bekuz007/hydrodesk-base/doku/Steckbrief_HydroDesk_Base.docx

Steckbrief zu Projekt HydroDesk Base

Betreuer: ________________ Gruppenmitglieder: _______________________________________________________

Problem / Szenario / Projekt:

Welches Thema? Wie lautet die Projektidee?
Wo begegnet mir das Thema / Problem in meinem Alltag?

Thema: IoT-Schreibtisch-Gadget zur Trinkmengen-Erfassung (HydroDesk Base).

Projektidee: Ein flaches, rechteckiges ESP32-Gerät (180 × 100 × 25 mm) für den Schreibtisch. Links sitzt das Board CYD ESP32-2432S028R mit 2,8″-Touch-Display, rechts ein Flaschen-Pad (90 × 90 mm) mit Silikonmatte für jede normale Flasche. Eine Wägezelle misst das Gewicht; per Touch-Tasten „Leer“ und „Voll“ wird die Flasche kalibriert und die getrunkene Menge in ml berechnet. Das Display zeigt Tagesziel, Fortschritt und nächste Erinnerung, eine Lichtlinie vorne (COB-LED-Streifen hinter gedrucktem Diffusor) erinnert ans Trinken. Bei verschüttetem Wasser schaltet ein Feuchtigkeitssensor den Strom ab, ein Schalter trennt den Akku ab. Per Bluetooth LE verbindet sich das Gerät mit einer Android-App (Supabase). Optional: Telegram.

Alltag: Am Schreibtisch oder in der Schule steht die Flasche oft da, aber man vergisst zu trinken. Fertige Smart-Flaschen sind teuer und an eine Marke gebunden. HydroDesk Base funktioniert mit jeder Flasche und ist täglich sichtbar.

Handlungsprodukt:

Was ist das Endprodukt? Welche Konfigurationen sollen am Ende gemacht sein?

Endprodukt: Funktionsfähiger Prototyp im 3D-gedruckten Gehäuse (Display links, Flaschen-Pad rechts, Lichtlinie vorne, Ein/Aus-Schalter links, abnehmbare USB-Kappe), live vorführbar, plus Android-App, Quellcode im Git-Repo, CAD-Datei, Lasten-/Pflichtenheft, Testprotokoll und Bericht.

Am Ende konfiguriert:

• WLAN und optional Telegram-Token in secrets.h (nicht im Repo), BLE-Kopplung zur App

• Flaschen-Kalibrierung per Touch: „Leer“ (leere Flasche) und „Voll“ (volle Flasche)

• Kalibrierung der Wägezelle (Tara, Leer- und Vollgewicht dauerhaft speichern)

• Feuchtigkeits-Schwelle: bei Nässe → LED-Strom aus und Sperrbildschirm „WASSER ERKANNT · STROM AUS“

• Lichtlinie vorne (COB-LED-Streifen WS2812B, 26 LEDs, Diffusor): blau = Erinnerung, grün = Ziel erreicht, rot = Akku / Fehler, bei Nässe aus

• Optional Bot-Befehle: /status, /ziel, /hilfe

Gruppenzusammensetzung

Wie viele Schüler werden gemeinsam an dem Projekt arbeiten?
Wer könnte welche Aufgabe übernehmen?

2 Schüler, ca. 50 Stunden inkl. Dokumentation (je 25 h).

Person A: Hardware, Verkabelung, Wägezelle (HX711), Feuchtigkeitssensor, Stromversorgung (LiPo, USB-C, Ein/Aus-Schalter, Sicherheitsabschaltung), rechteckiges Gehäuse (CAD + 3D-Druck), Zustandsautomat.

Person B: Touch-Display und Bedienoberfläche, WLAN/NTP, optionale Telegram-Anbindung, Leer/Voll-Kalibrierung, Doku-Leitung.

Gemeinsam: Planung, Integration, Tests, Bericht, Präsentation.

Konkretisierung der Inhalte

Welche einzelnen Inhalte sind relevant?
Welche Konfigurationen / Techniken werden angewandt?
Welche Schritte werden erwartet?
Was ist die Ziel- / Endkonfiguration?

Inhalte: Mikrocontroller-Programmierung in C/C++, Sensorik (Wägezelle, Feuchtigkeitseingang), Touch-Bedienoberfläche, Zustandsautomat (UML), Bluetooth LE, Android-App, optional Telegram, Umgang mit Zugangsdaten, Git, CAD, Testen und Dokumentieren.

Techniken: PlatformIO (Arduino), CYD ESP32-2432S028R (2,8″-Touch), HX711 + Wägezelle 5 kg, COB-LED-Streifen WS2812B mit Diffusor, LiPo + TC4056/USB-C + Pololu S13V10F5, Nässe-Abschaltung (Regensensor + AO3401A), Ein/Aus-Schalter, Stromsparen, Bluetooth LE, Android-App (Kotlin, Supabase), OpenSCAD.

Schritte: 1. Lasten-/Pflichtenheft, Zustandsdiagramm 2. Entwicklungsumgebung, Sensor- und Display-Test 3. Wäge-Kalibrierung (Leer/Voll) 4. Feuchtigkeits-Sicherheitsabschaltung 5. Bedienoberfläche, Bluetooth LE + Android-App, optional Telegram 6. Gehäuse konstruieren, drucken, Integration 7. Tests 8. Doku und Präsentation

Zielkonfiguration: Gerät 180 × 100 × 25 mm mit Akku, USB-C-Laden und Ein/Aus-Schalter; Flasche abstellen → ml-Anzeige wenige Sekunden nach der Leer/Voll-Kalibrierung; bei Wasser Strom aus und Sperrbildschirm; Erinnerung per Lichtlinie, Daten per BLE in der App; Akkulaufzeit geschätzt ca. 27–54 h.

Benötigte Materialien

Welche Ausstattung benötigen die Schüler für die Durchführung?
Welche Materialien müssten seitens der Schule / des Betreuers gestellt werden?

Schüler: Laptop mit VS Code + PlatformIO, Android Studio, OpenSCAD; Android-Smartphone, Handy-Hotspot für die Demo, GitHub-Account.

Von Schule / Betreuer (ca. 142 € laut Vorkalkulation, ca. 125 € ohne PLA): CYD ESP32-2432S028R, Wägezelle 5 kg + HX711, COB-LED-Streifen, Regensensor, FET-Platine + Ein/Aus-Schalter, LiPo + TC4056 + Pololu S13V10F5, Silikonmatte, Kleinteile, Messschieber, Lötstation; 3D-Druck des Gehäuses; optional Breadboard.

Hinweis: Es wird keine Smart-Flasche gekauft – jede vorhandene Flasche dient zur Demo.
