bekuz007/hydrodesk-base/gehaeuse/preview/01_zusammenbau_iso.png

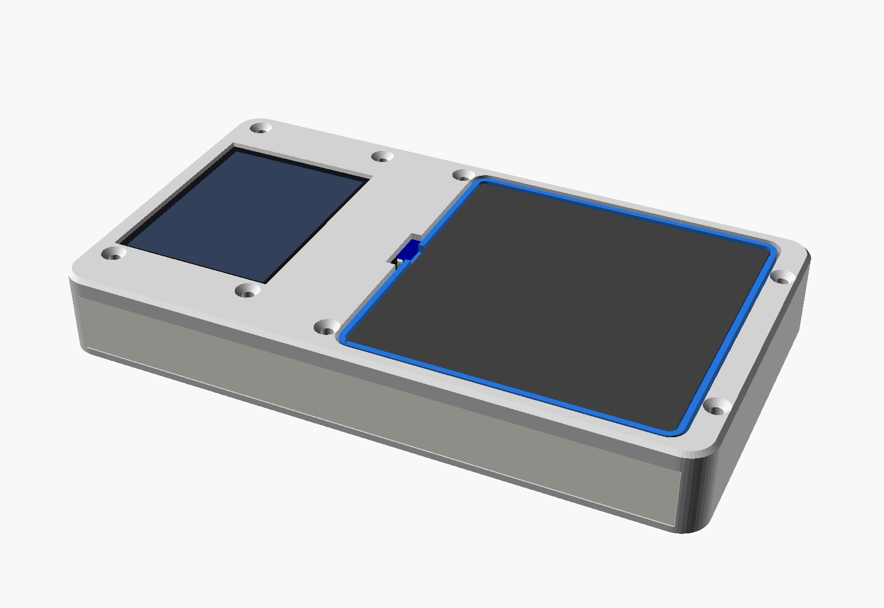
gehaeuse/preview/01_zusammenbau_iso.png
