bekuz007/hydrodesk-base/gehaeuse/preview/02_explosionsansicht.png

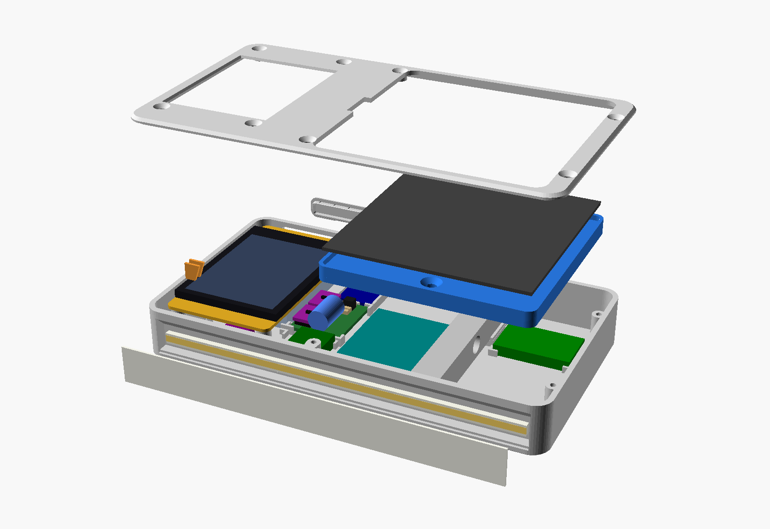
gehaeuse/preview/02_explosionsansicht.png
