bekuz007/hydrodesk-base/gehaeuse/preview/03_draufsicht.png

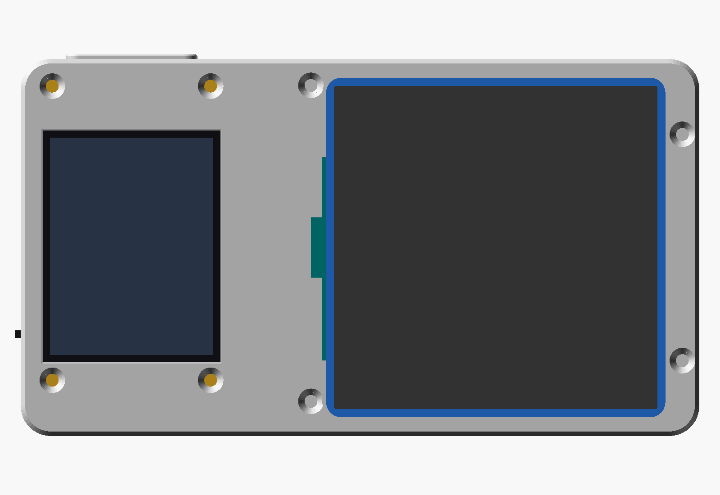
gehaeuse/preview/03_draufsicht.png
