bekuz007/hydrodesk-base/gehaeuse/preview/04_innen_ohne_deckel.png

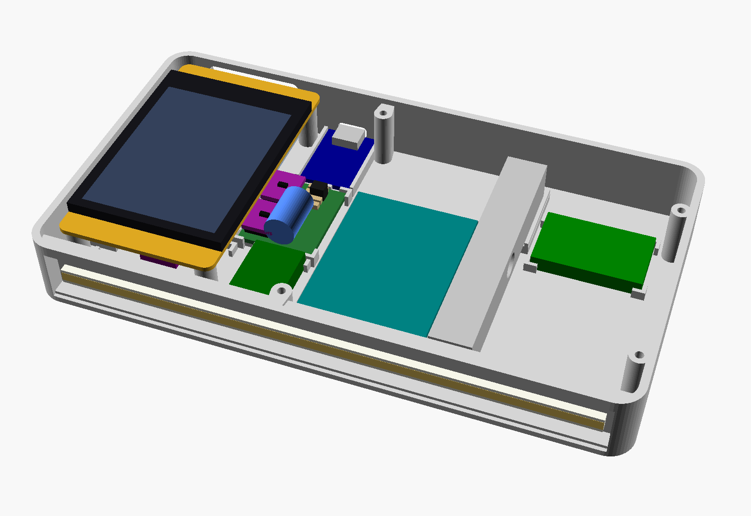
gehaeuse/preview/04_innen_ohne_deckel.png
