bekuz007/hydrodesk-base/gehaeuse/preview/05_innen_draufsicht.png

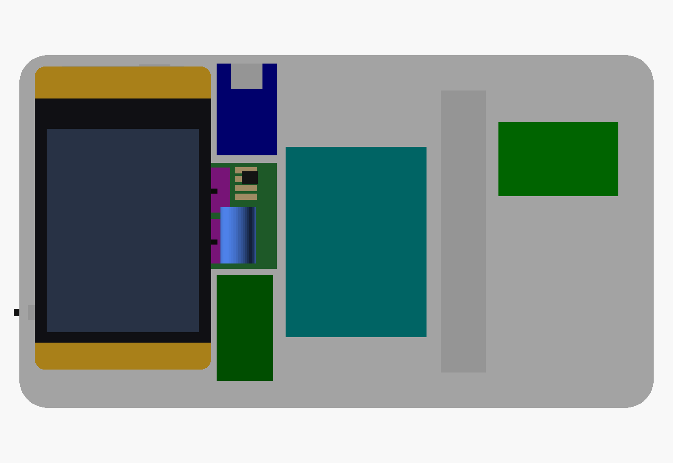
gehaeuse/preview/05_innen_draufsicht.png
