bekuz007/hydrodesk-base/gehaeuse/preview/06_rueckseite_usb.png

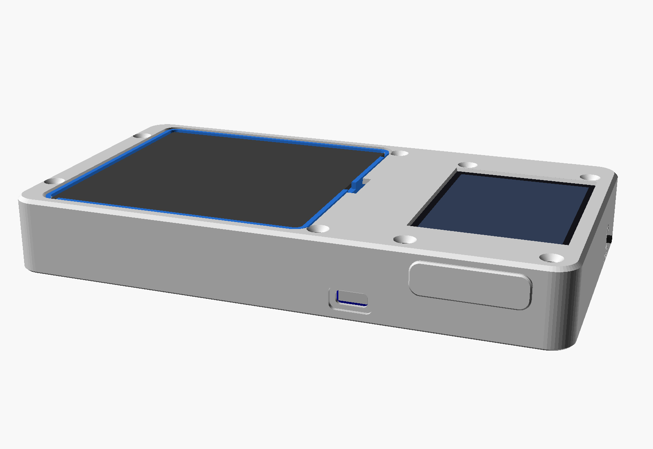
gehaeuse/preview/06_rueckseite_usb.png
