bekuz007/hydrodesk-base/gehaeuse/preview/07_front_led.png

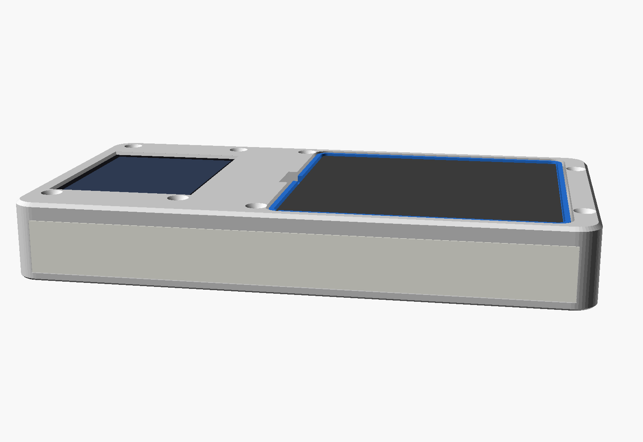
gehaeuse/preview/07_front_led.png
