bekuz007/hydrodesk-base/gehaeuse/preview/08_schnitt.png

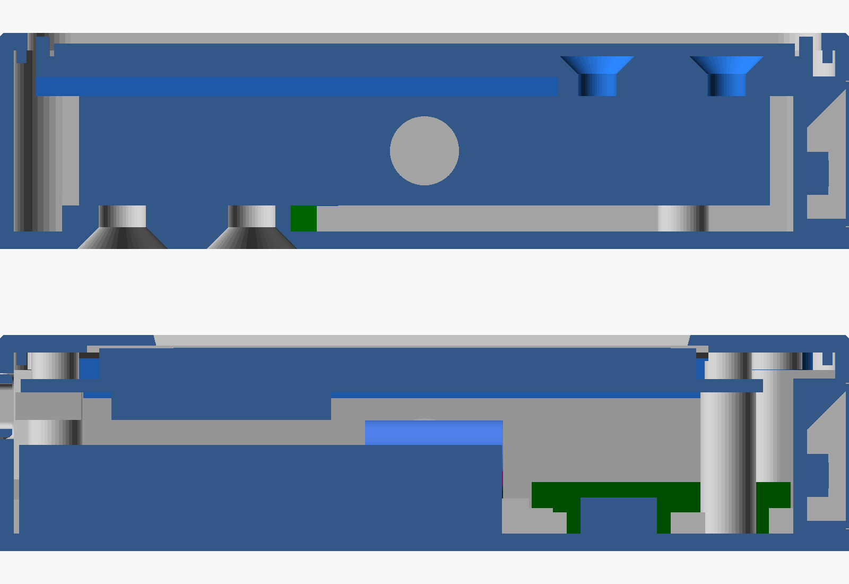
gehaeuse/preview/08_schnitt.png
