bekuz007/hydrodesk-base/gehaeuse/preview/10_teil_base.png

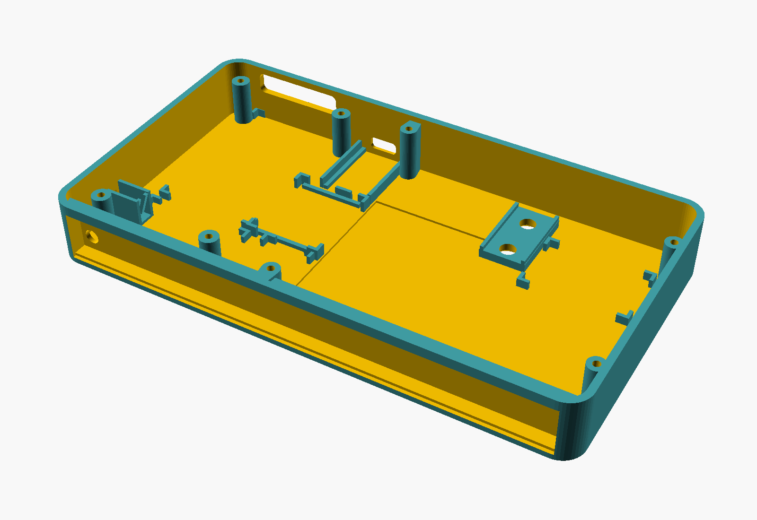
gehaeuse/preview/10_teil_base.png
