bekuz007/hydrodesk-base/gehaeuse/preview/11_teil_base_unterseite.png

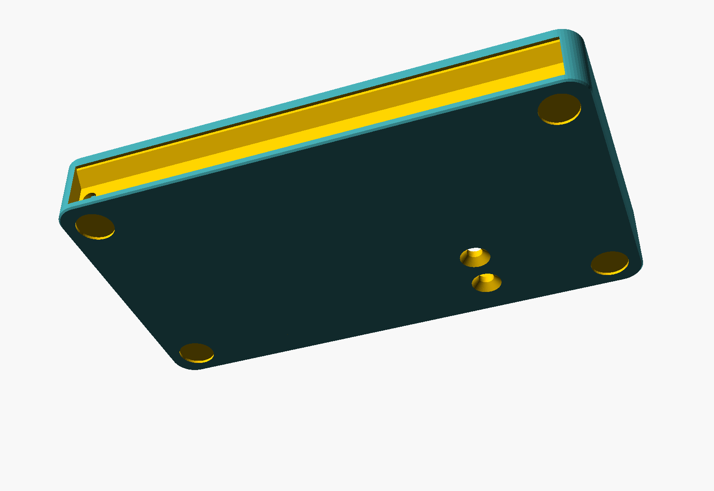
gehaeuse/preview/11_teil_base_unterseite.png
