bekuz007/hydrodesk-base/gehaeuse/preview/12_teil_cover_druckLage.png

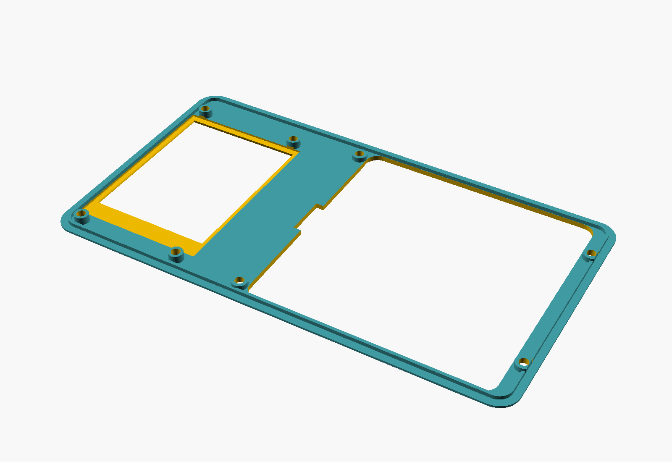
gehaeuse/preview/12_teil_cover_druckLage.png
