bekuz007/hydrodesk-base/gehaeuse/preview/13_teil_pad_oben.png

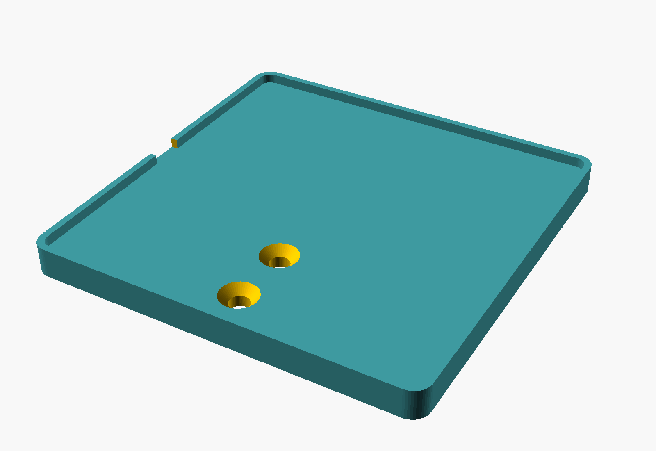
gehaeuse/preview/13_teil_pad_oben.png
