bekuz007/hydrodesk-base/gehaeuse/preview/14_teil_pad_unterseite.png

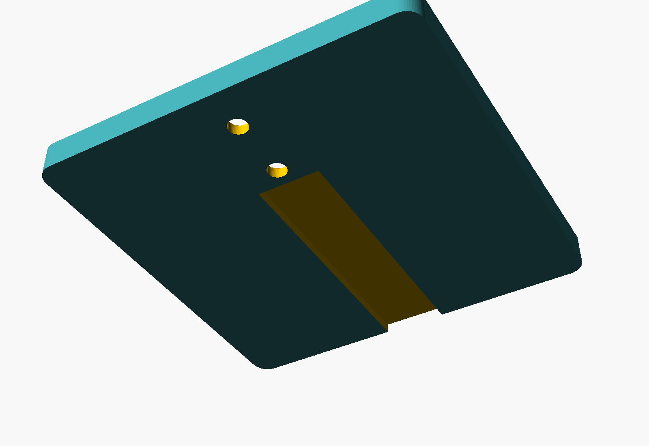
gehaeuse/preview/14_teil_pad_unterseite.png
