bekuz007/hydrodesk-base/gehaeuse/preview/15_teil_kappe_druckLage.png

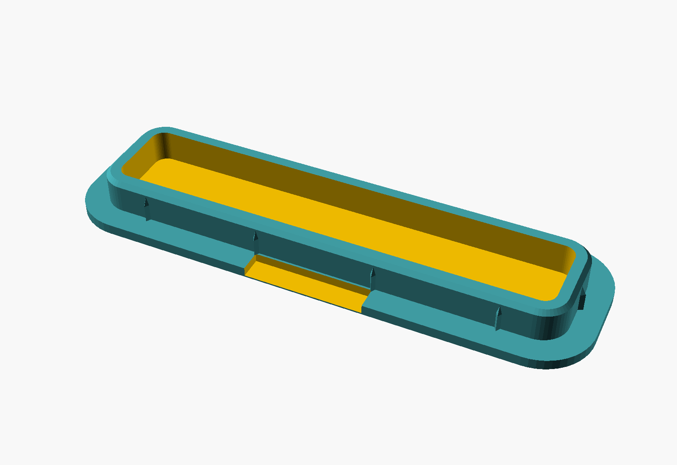
gehaeuse/preview/15_teil_kappe_druckLage.png
