bekuz007/hydrodesk-base/gehaeuse/preview/17_teil_diffusor_druckLage.png

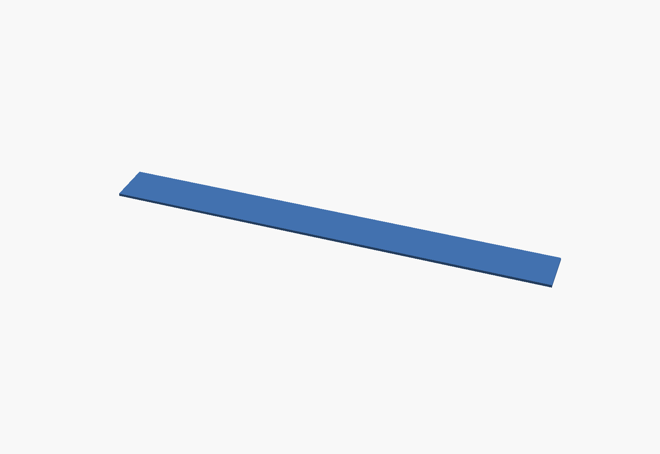
gehaeuse/preview/17_teil_diffusor_druckLage.png
