bekuz007/hydrodesk-base/gehaeuse/preview/19_teil_keile_druckLage.png

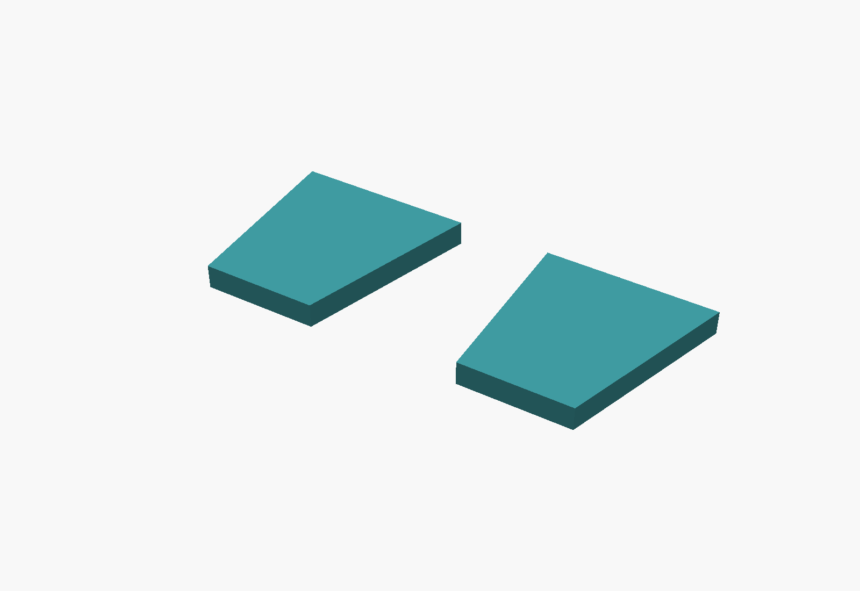
gehaeuse/preview/19_teil_keile_druckLage.png
