bekuz007/hydrodesk-base/gehaeuse/preview/21_schalter_tasche_schnitt.png

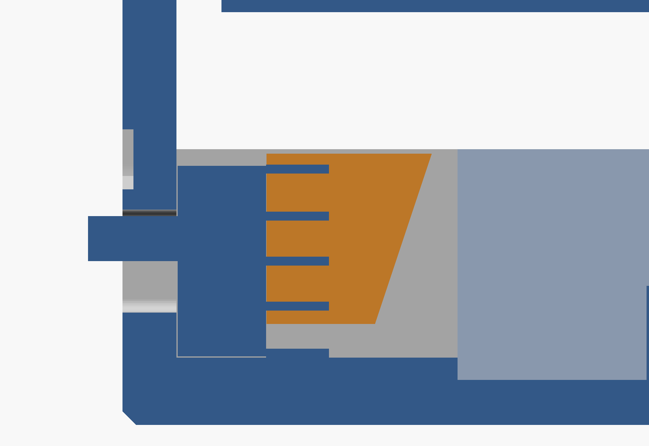
gehaeuse/preview/21_schalter_tasche_schnitt.png
