bekuz007/hydrodesk-base/gehaeuse/preview/22_schalter_tasche_innen.png

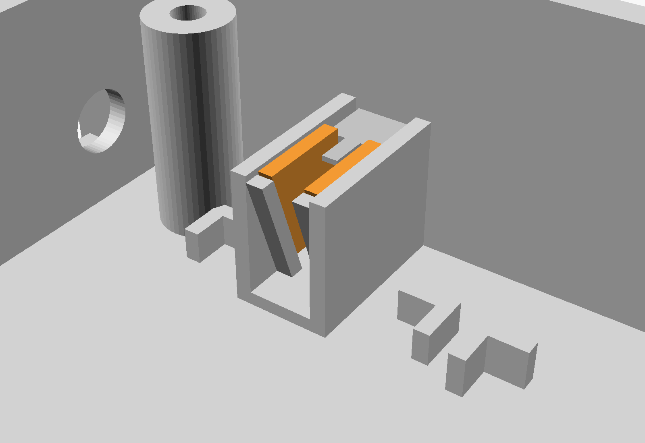
gehaeuse/preview/22_schalter_tasche_innen.png
