bekuz007/hydrodesk-base/gehaeuse/preview/diffusor_eingesetzt.png

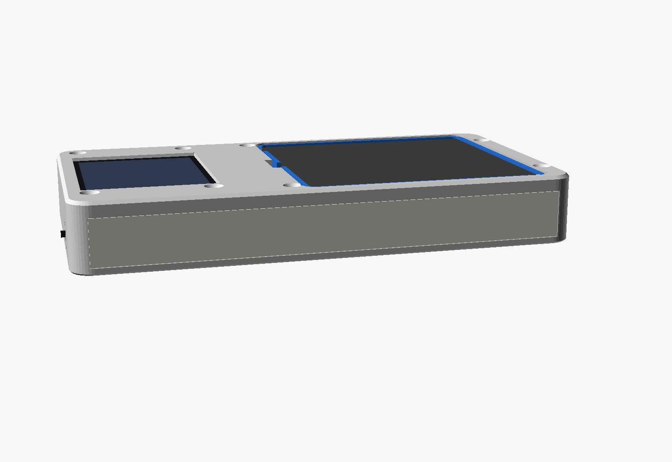
gehaeuse/preview/diffusor_eingesetzt.png
