bekuz007/hydrodesk-base/design/visualisierung/src/w_cover.scad

use <../../../gehaeuse/hydrodesk_base.scad>
cover();
