bekuz007/hydrodesk-base/design/visualisierung/src/w_diff.scad

use <../../../gehaeuse/hydrodesk_base.scad>
diffusor();
