bekuz007/hydrodesk-base/design/visualisierung/src/w_keil.scad

use <../../../gehaeuse/hydrodesk_base.scad>
for (s=[-1,1]) keil(s);
