bekuz007/hydrodesk-base/design/visualisierung/src/w_pad.scad

use <../../../gehaeuse/hydrodesk_base.scad>
pad();
